Daamin909/keyboard-v2/assets/front_3d.png

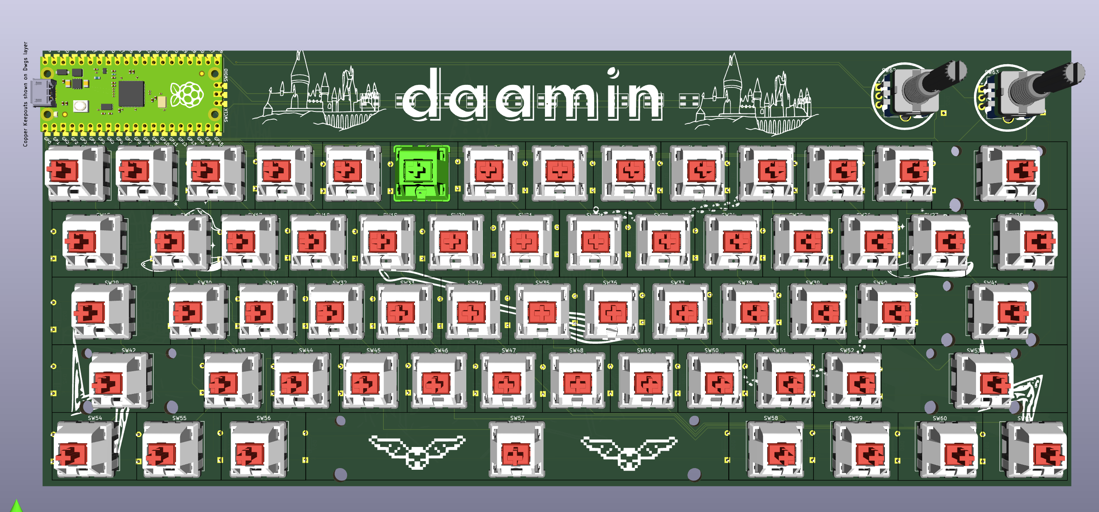
assets/front_3d.png
