Daamin909/keyboard-v2/assets/new.png

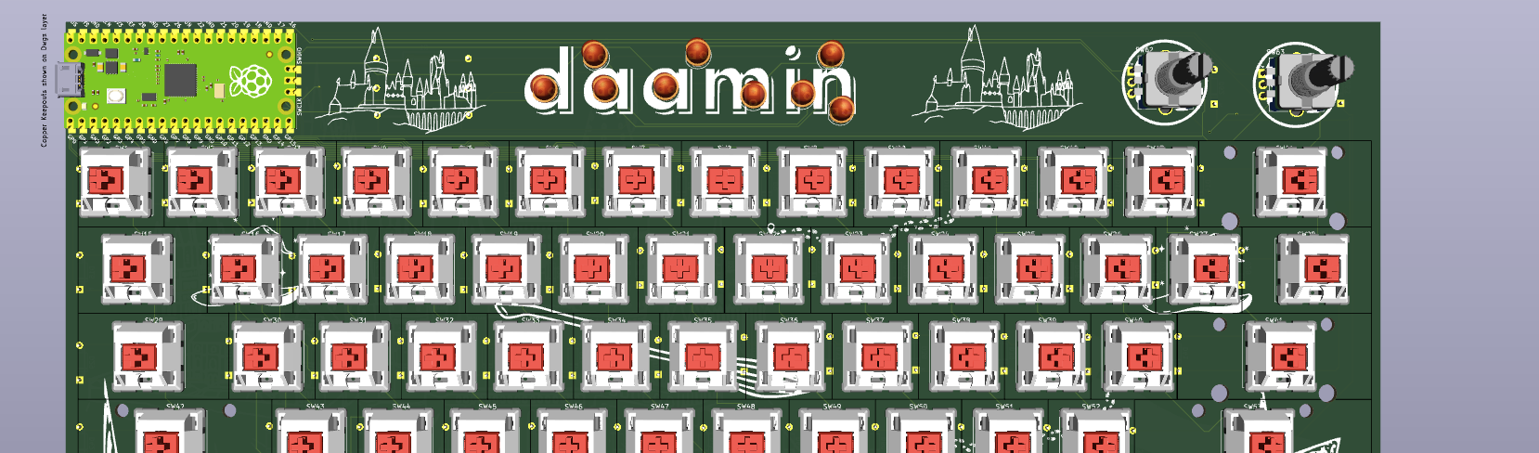
assets/new.png
